udu3324/slider-synth/firmware/slider_synth/src/DAC_MCP49xx.h

#ifndef _DAC_MCP49xx_H
#define _DAC_MCP49xx_H

//#define AVR
#include <Arduino.h>
#include <SPI.h>
#ifdef AVR
#include <Arduino.h>
#endif
#include <inttypes.h>

#ifndef _SPI_H_INCLUDED
#error Please include SPI.h before DAC_MCP49xx.h!
#endif

// Microchip MCP4901/MCP4911/MCP4921/MCP4902/MCP4912/MCP4922 DAC driver
// Thomas Backman, 2012

class DAC_MCP49xx {
  public:

  // These are the DAC models we support
  enum Model {
    MCP4901 = 1, /* single, 8-bit */
    MCP4911,     /* single, 10-bit */
    MCP4921,     /* single, 12-bit */
    MCP4902,     /* dual, 8-bit */
    MCP4912,     /* dual, 10-bit */
    MCP4922      /* dual, 12-bit */
  };

  enum Channel {
	  CHANNEL_A = 0,
	  CHANNEL_B = 1
  };
    
  DAC_MCP49xx(Model _model, int _ss_pin);
  void setBuffer(boolean _buffer);
  void setPortWrite(boolean _port_write);
  boolean setGain(int _gain);
  //boolean setSPIDivider(int _spi_divider);
  void shutdown(void);

  /* All of these call _output() internally */
  void output(unsigned short _out);
  void outputA(unsigned short _out); /* same as output(), but having A/B makes more sense for dual DACs */
  void outputB(unsigned short _out);
  void output2(unsigned short _out, unsigned short _out2); // For MCP49x2


  void init(); //Start the SPI
  void init(SPIClass * _spi); // Start with another SPI

  private:
    void _output(unsigned short _out, Channel _chan);
    int ss_pin;
    int bitwidth;
    boolean bufferVref;
    boolean gain2x; /* false -> 1x, true -> 2x */
    boolean port_write; /* use optimized port writes? won't work everywhere! */
    int spi_divider;
    SPIClass * dac_spi;
};

#endif
